promesoft/KicadJE_EffectsUnit1/20190326_193637.jpg

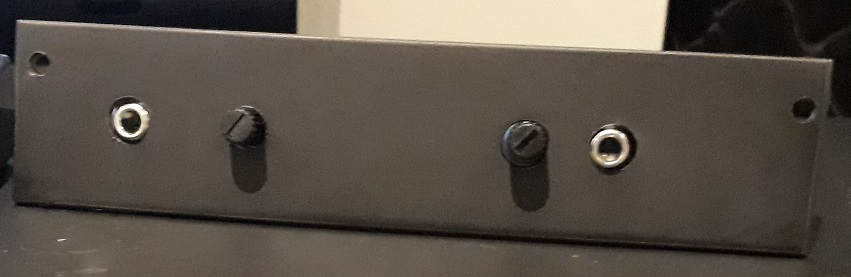
20190326_193637.jpg
