promesoft/KicadJE_EffectsUnit1/20190326_193828.jpg

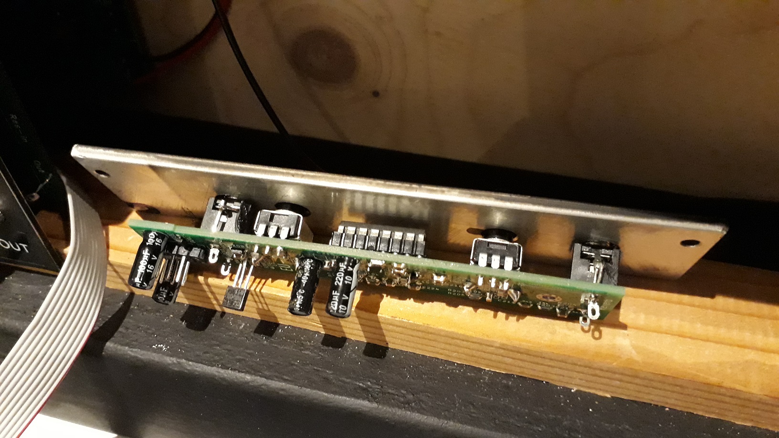
20190326_193828.jpg
